danpham/nixie_clock/software/nixie_clock_esp32_project/components/uart/uart.c

/******************************************************************
 * 1. Included files (microcontroller ones then user defined ones)
******************************************************************/
#include "uart.h"
#include <string.h>


/******************************************************************
 * 2. Define declarations (macros then function macros)
******************************************************************/


/******************************************************************
 * 3. Typedef definitions (simple typedef, then enum and structs)
******************************************************************/


/******************************************************************
 * 4. Variable definitions (static then global)
******************************************************************/


/******************************************************************
 * 5. Functions prototypes (static only)
******************************************************************/


/******************************************************************
 * 6. Functions definitions
******************************************************************/
void uart_init(void)
{
    uart_config_t uart_config = {
        .baud_rate = UART_BAUD_RATE,
        .data_bits = UART_DATA_8_BITS,
        .parity    = UART_PARITY_DISABLE,
        .stop_bits = UART_STOP_BITS_1,
        .flow_ctrl = UART_HW_FLOWCTRL_DISABLE
    };

    // Configure UART
    uart_param_config(UART_PORT, &uart_config);

    // Configure TX/RX pins
    uart_set_pin(UART_PORT, UART_TX_PIN, UART_RX_PIN, UART_PIN_NO_CHANGE, UART_PIN_NO_CHANGE);

    // Install driver
    uart_driver_install(UART_PORT, UART_BUF_SIZE, UART_BUF_SIZE, 0, NULL, 0);
}

void uart_write(const char *str, size_t len)
{
    uart_write_bytes(UART_PORT, str, len);
}
