danpham/nixie_clock/software/nixie_clock_esp32_project/components/hv5622/hv5622_mock.h

#ifndef HV5622_MOCK_H
#define HV5622_MOCK_H

#include <stdint.h>
#include <stdbool.h>

extern uint64_t last_sent_data;

void hv5622_init(void);
void hv5622_send64(uint64_t data);
void hv5622_set_output(int pin, bool value);

#endif // HV5622_MOCK_H
